papamidas/ATU_0_HW/DSC_1715.JPG

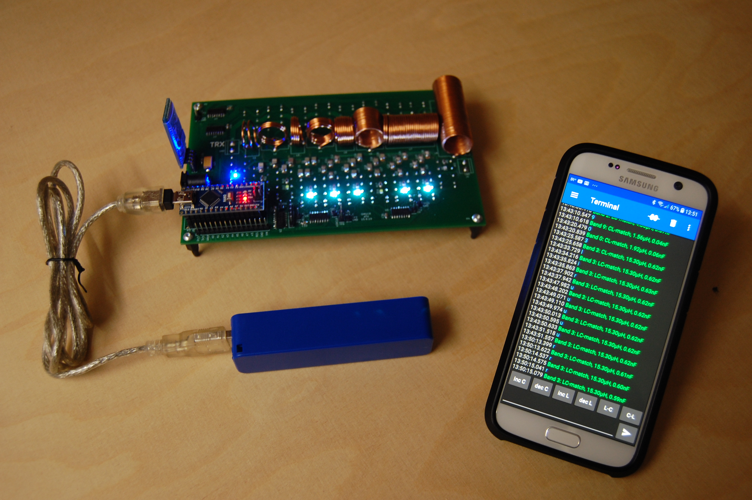
DSC_1715.JPG
